MOSH-Insa-Toulouse/2022-2023-4gp-bourguet-cuzacq/Application/app_face_avant.png

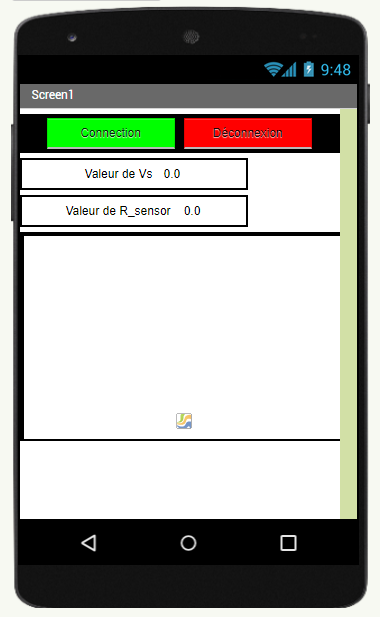
Application/app_face_avant.png
