MOSH-Insa-Toulouse/2022-2023-4gp-bourguet-cuzacq/Application/app_page_1.png

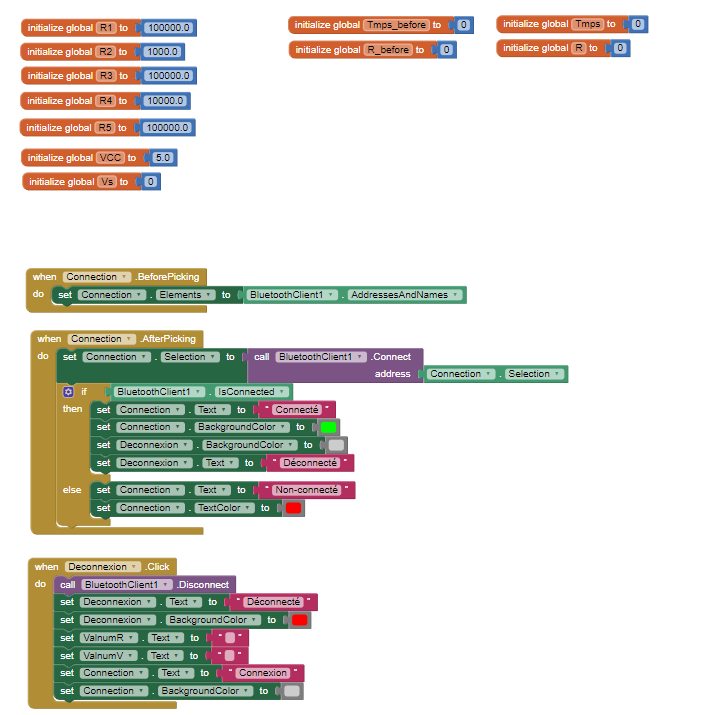
Application/app_page_1.png
