MOSH-Insa-Toulouse/2022-2023-4gp-bourguet-cuzacq/imagesRapport/image 5.jpg

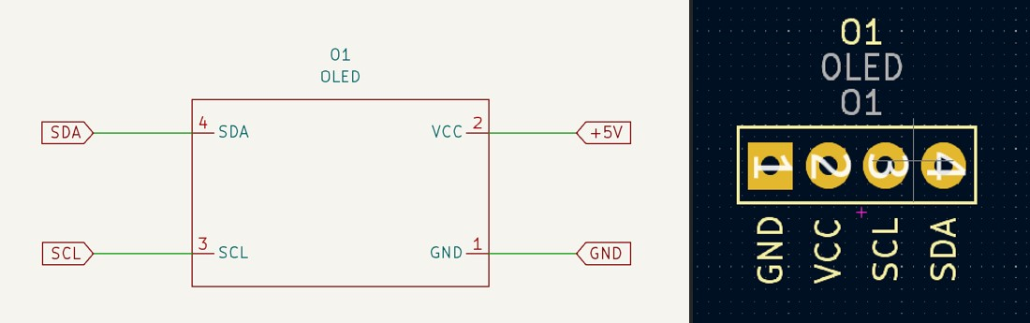
imagesRapport/image 5.jpg
