MOSH-Insa-Toulouse/2022-2023-4gp-bourguet-cuzacq/imagesRapport/image 15.jpg

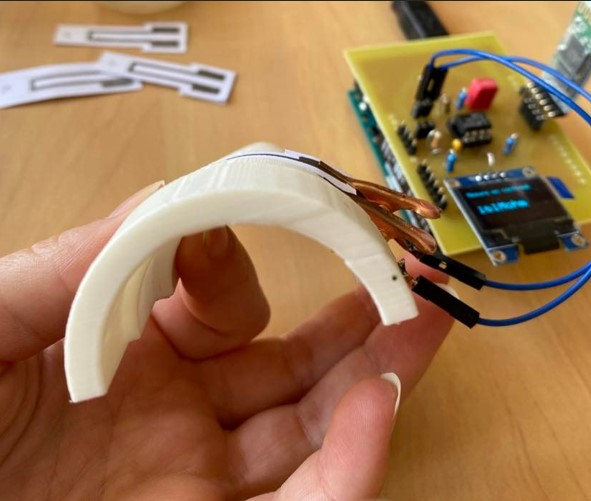
imagesRapport/image 15.jpg
